alr46664/Access_Control/Project.h

#ifndef _PROJECT_H
#define _PROJECT_H

#ifndef ULONG_MAX
#define ULONG_MAX 4294967295
#endif

#ifndef null
#define null NULL
#endif

// uncomment below to enter DEBUG_MODE (Arduino-PC Serial begin)
#define DEBUG_MODE 1



#endif  // _PROJECT_H
